marangisto/VCA/VCA.asc

C1: cap; 2.2nF
C2: cap; 2.2nF
D1: diode; 1N4148
D2: diode; 1N4148
D3: diode; 1N4148
D4: LED; AOT-2015
I1: current; PWL(0 0 2m 0 8m 1m)
Q1: pnp; 2N2907
Q2: npn; 2N2222
R1: res; 980
R2: res; 1020
R3: res; 4.7k
R4: res; 235k
R5: res; 33k
R6: res; 68k
R7: res; 1k
R8: res; 100k
R9: res; 33k
R10: res; 50k
R11: res; 10k
R12: res; 50k
R13: res; 9.1k
R14: res; 150k
R15: res; 4.7k
R16: res; 235k
R17: res; 33k
R18: res; 980
R19: res; 1020
R20: res; 68k
R21: res; 4.7k
R22: res; 4.7k
R23: res; 100k
R24: res; 150k
R26: res; 47k
R27: res; 47k
R28: res; 680
R29: res; 130k
R30: res; 10k
R31: res; 1k
R32: res; 100k
R33: res; 33k
R34: res; 100k
R35: res; 1
R36: res; 1k
U1: LM13700
U2: LM13700
U4: opamp2; TL071
U5: opamp2; TL071
V1: voltage; 12
V2: voltage; SINE(0 5 5k); AC 1m
V3: voltage; -12
Vcv: voltage; PWL(0 0 1m 0 9m 5); AC 5
Named nets: 0, VCC, VSS, Vin, Vout, CMN, Vcv
.lib lm13700.sub
.tran 1u 10m
.include TL071.mod
;.ac dec 1u 1 1000k
