marangisto/VCA/VCA-JFET.asc

D1: diode; 1N914
J1: njf; 2SK170
J2: njf; 2SK170
Q1: pnp; 2N3906
R1: res; 1k
R2: res; 47k
R3: res; 680
R4: res; 22k
R5: res; 1000k
R6: res; 100k
R7: res; 10k
R8: res; 1k
R9: res; 47k
R10: res; 100k
R11: res; 1k
R12: res; 100k
U1: opamp2; TL071
U2: opamp2; TL071
U3: opamp2; TL071
V1: voltage; 12V
V2: voltage; 12V
Vcv: voltage; 0
Vin: voltage; 5
Named nets: 0, OUT, V+, V-
.include TL071.mod
;op
.include 2SK170.mod
.dc Vcv -1 5 .01 Vin -5 5 0.5
